electricwool/Brother-PPD/Kicad/PPD.kicad_sch

## KiCad design Kicad/PPD.kicad_sch (2026-01-25)

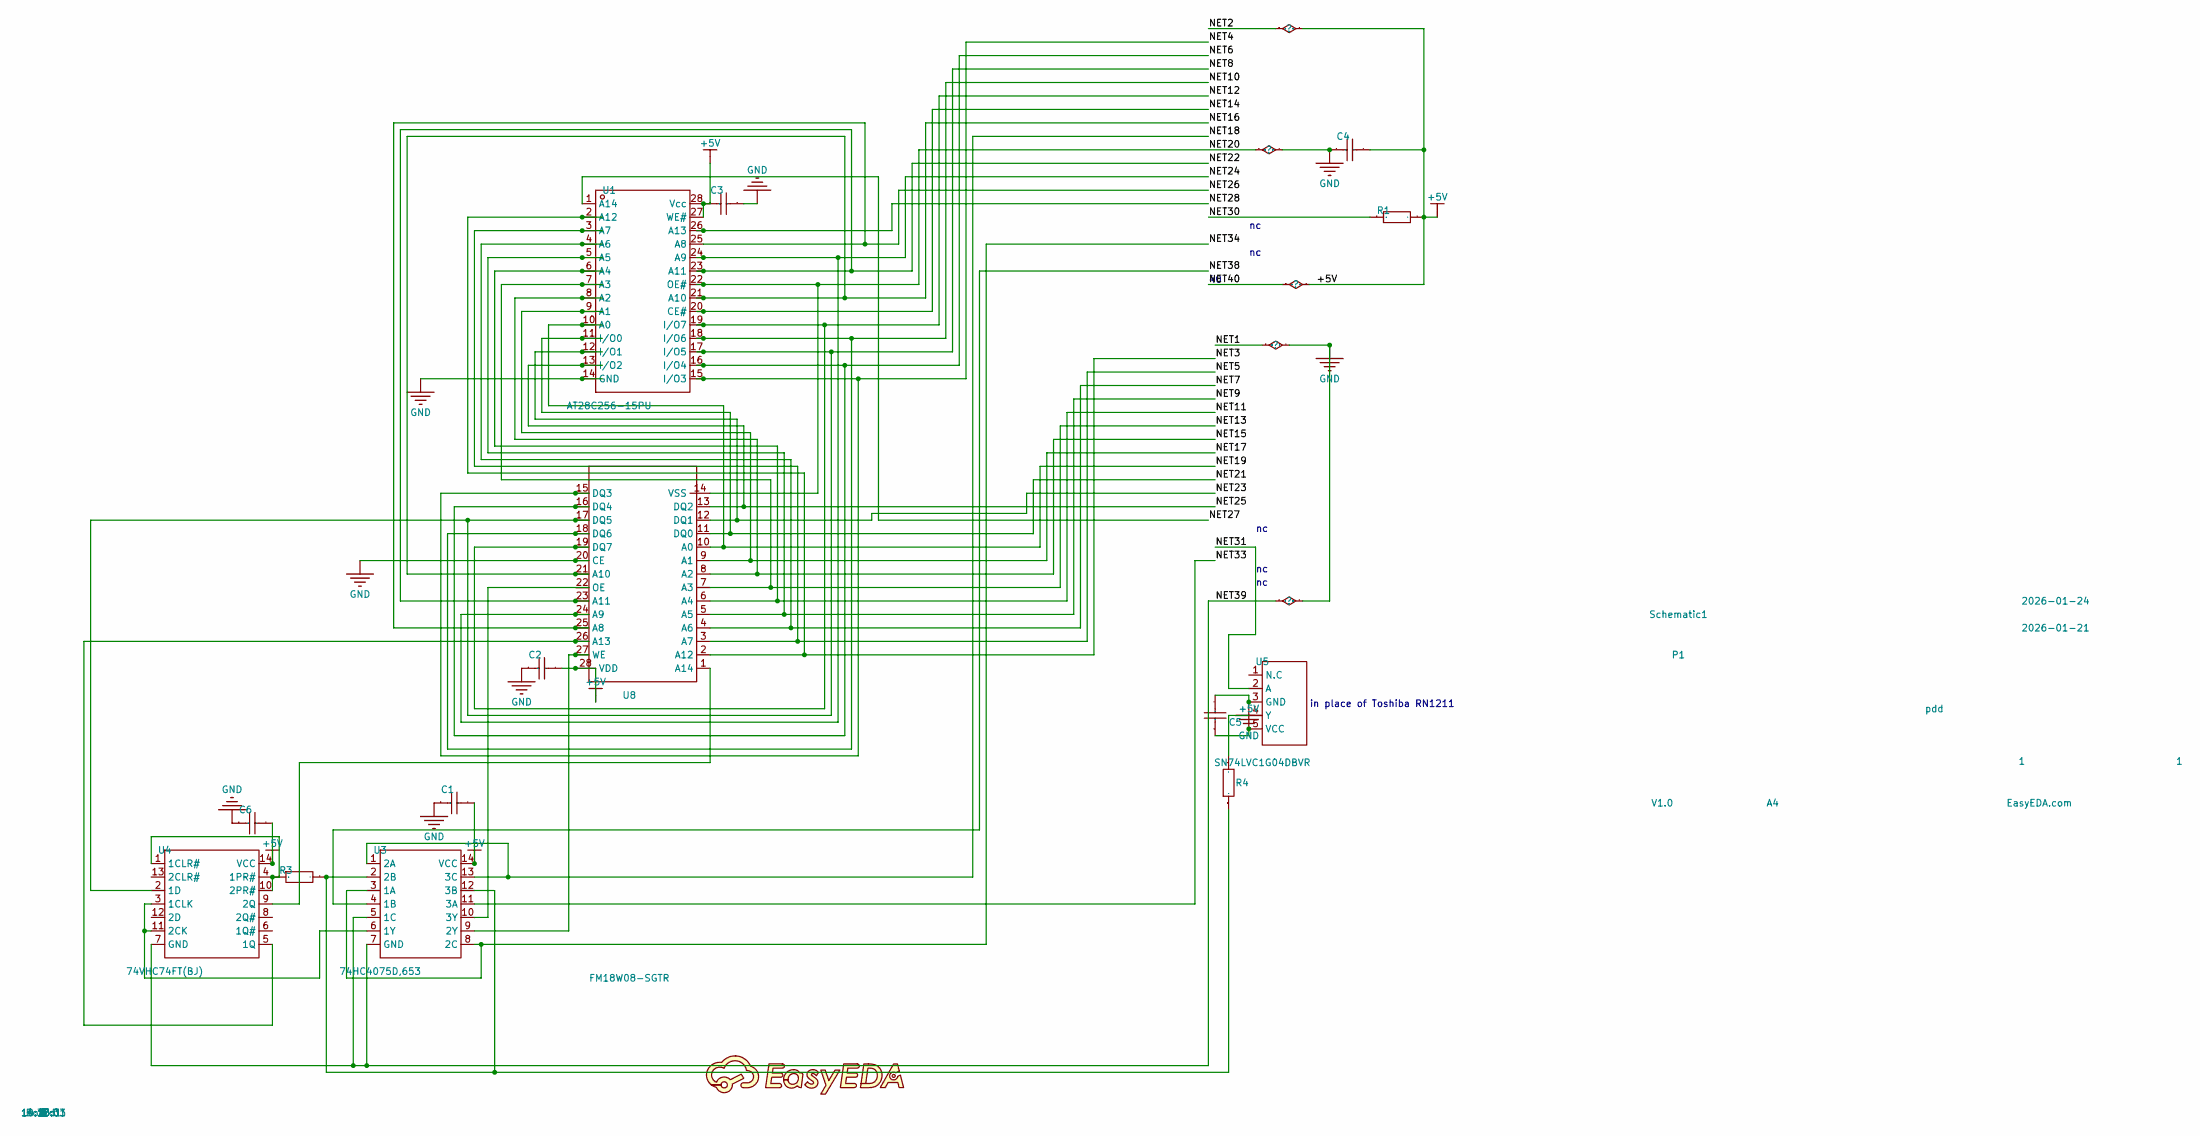
[picture p2: schematic PPD.kicad_sch]

Parts:
C1, C2, C3, C4, C5, C6: 100nF; C0603; Manufacturer Part CL10B104JB8NNNC; LCSC Part Name 100nF ±5% 50V
R1: 10kΩ; R0805; Manufacturer Part RT0805BRD0710KL; LCSC Part Name 薄膜电阻 10kΩ ±0.1% 125mW
R3, R4: 4.7kΩ; R0805; Manufacturer Part 0805W8F4701T5E; LCSC Part Name 4.7kΩ ±1% 125mW 厚膜电阻
U1: AT28C256-15PU; PDIP-28_L37.0-W13.5-P2.54-LS15.6-BL; Manufacturer Part AT28C256-15PU; LCSC Part Name AT28C256 15PU
U3: 74HC4075D,653; SO-14_L8.9-W3.9-P1.27-LS6.0-BL; Manufacturer Part 74HC4075D,653; LCSC Part Name 74HC4075D,653
U4: 74VHC74FT(BJ); TSSOP-14_L5.0-W4.4-P0.65-LS6.5-BL; Manufacturer Part 74VHC74FT(BJ); LCSC Part Name 74VHC74FT(BJ)
U5: SN74LVC1G04DBVR; SOT-23-5_L3.0-W1.7-P0.95-LS2.8-BR; Manufacturer Part SN74LVC1G04DBVR; LCSC Part Name 单路反向器
U8: FM18W08-SGTR; SOIC-28_L18.0-W7.5-P1.27-LS10.3-BL; Manufacturer Part FM18W08-SGTR; LCSC Part Name FM18W08-SGTR

Connections:
+5V: C4.2, R1.2
NET3: U1.2 (A12), U8.2 (A12)
NET4: U1.15 (I/O3), U8.15 (DQ3)
NET5: U1.3 (A7), U8.3 (A7)
NET6: U1.16 (I/O4), U8.16 (DQ4)
NET7: U1.4 (A6), U8.4 (A6)
NET8: U1.17 (I/O5), U4.2 (1D), U8.17 (DQ5)
NET9: U1.5 (A5), U8.5 (A5)
NET10: U1.18 (I/O6), U8.18 (DQ6)
NET11: U1.6 (A4), U8.6 (A4)
NET12: U1.19 (I/O7), U8.19 (DQ7)
NET13: U1.7 (A3), U8.7 (A3)
NET14: U1.20 (CE#)
NET15: U1.8 (A2), U8.8 (A2)
NET16: U1.21 (A10), U8.21 (A10)
NET17: U1.9 (A1), U8.9 (A1)
NET18: U3.1 (2A), U3.13 (3C)
NET19: U1.10 (A0), U8.10 (A0)
NET20: U1.22 (OE#), U8.14 (VSS)
NET21: U1.11 (I/O0), U8.11 (DQ0)
NET22: U1.23 (A11), U8.23 (A11)
NET23: U1.12 (I/O1), U8.12 (DQ1)
NET24: U1.24 (A9), U8.24 (A9)
NET25: U1.13 (I/O2), U8.13 (DQ2)
NET26: U1.25 (A8), U8.25 (A8)
NET27: U1.1 (A14)
NET28: U1.26 (A13)
NET30: R1.1
NET31: U5.2 (A)
NET33: U3.11 (3A)
NET34: U3.3 (1A), U3.8 (2C)
NET38: U3.4 (1B)
NET39: U3.5 (1C), U3.7 (GND), U4.7 (GND)
unnamed: C1.2, U3.14 (VCC)
unnamed: C2.2, U8.28 (VDD)
unnamed: C3.1, U1.27 (WE#), U1.28 (Vcc)
unnamed: C5.1, U5.5 (VCC)
unnamed: C5.2, U5.3 (GND)
unnamed: C6.2, U4.14 (VCC)
unnamed: R3.1, U4.1 (1CLR#), U4.4 (1PR#), U4.10 (2PR#)
unnamed: R3.2, R4.1, U3.2 (2B), U3.12 (3B)
unnamed: R4.2, U5.4 (Y)
unnamed: U3.6 (1Y), U4.3 (1CLK), U4.11 (2CK)
unnamed: U3.9 (2Y), U8.27 (WE)
unnamed: U4.5 (1Q), U8.26 (A13)
unnamed: U4.9 (2Q), U8.1 (A14)

Notes on the sheet:
in place of Toshiba RN1211
